SmartFarmingFutureOfAgriculture/Soil-Monitoring-Device/hardware/housing/8-Gehäuse-Mit-Elektronik_Bottom.jpg

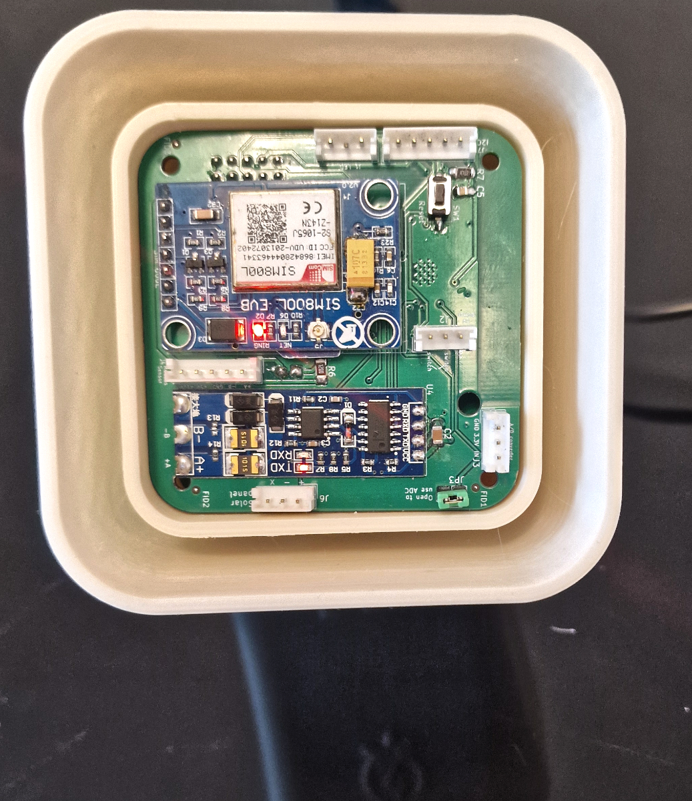
hardware/housing/8-Gehäuse-Mit-Elektronik_Bottom.jpg
