SmartFarmingFutureOfAgriculture/Soil-Monitoring-Device/software/src/config.cpp

/*
 * Smart Farming Soil Monitoring System
 * Copyright (C) 2024 Smart Farming gGmbH
 *
 * This software is released under the GNU General Public License v2 (GPL-2.0).
 * You are free to use, modify, and distribute it under the terms of this license.
 *
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
 * See the full license at: https://www.gnu.org/licenses/old-licenses/gpl-2.0.en.html
 */

#include "config.h"

// Definition der globalen Variablen
const char *ssid = "o2-WLAN53";
const char *password = "3F8XM34AKS7JLUZ";
const char *server = "soilmonitoring.smart-farming.org";
const char *apiKey = "7tWaKE8JtJmm30tkNp7Z";
WiFiClientSecure client;
const char *dataUrl = "/api/sensor.php";
const int httpsPort = 443;

const char *root_ca = R"EOF(
-----BEGIN CERTIFICATE-----
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
bFtFbMxvLVPYu1MpA0N8E0xQerv3Y14=
-----END CERTIFICATE-----
-----BEGIN CERTIFICATE-----
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
00u/I5sUKUErmgQfky3xxzlIPK1aEn8=
-----END CERTIFICATE-----
-----BEGIN CERTIFICATE-----
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
jjxDah2nGN59PRbxYvnKkKj9
-----END CERTIFICATE-----)EOF";
